Casperdroid5/ATTiny-Keychain-Handheld/Potential OLED drivers/ssd1306xled-master/ssd1306xled_imgs1/main.c

/**
 * SSD1306xLED - Testing scripts
 * @author Neven Boyanov
 * This is part of the Tinusaur/SSD1306xLED project.
 * ----------------------------------------------------------------------------
 *  Copyright (c) 2021 Tinusaur (https://tinusaur.com). All rights reserved.
 *  Distributed as open source under the MIT License (see the LICENSE.txt file)
 *  Please, retain in your work a link to the Tinusaur project website.
 * ----------------------------------------------------------------------------
 * Source code available at: https://gitlab.com/tinusaur/ssd1306xled
 */

// ============================================================================

// NOTE: About F_CPU - it should be set in either (1) Makefile; or (2) in the IDE.

#include <stdint.h>
#include <avr/io.h>
#include <util/delay.h>

#include "tinyavrlib/cpufreq.h"

#include "ssd1306xled/ssd1306xled.h"
#include "ssd1306xled/ssd1306xledfx.h"

#include "img0s128x64c1.h"
#include "img1s128x64c1.h"

// ~~~~~~~~~~~~~~~~~~~~~~~~~~~~~~~~~~~~~~~~~~~~~~~~~~~~~~~~~~~~~~~~~~~~~~~~~~~~
//                 ATtiny85
//               +----------+    (-)--GND--
//      (RST)--> + PB5  Vcc +----(+)--VCC--
// ---[OWOWOD]---+ PB3  PB2 +----[TWI/SCL]-
// --------------+ PB4  PB1 +--------------
// --------(-)---+ GND  PB0 +----[TWI/SDA]-
//               +----------+
//                 Tinusaur
// ~~~~~~~~~~~~~~~~~~~~~~~~~~~~~~~~~~~~~~~~~~~~~~~~~~~~~~~~~~~~~~~~~~~~~~~~~~~~
// NOTE: If you want to reassign the SCL and SDA pins and the I2C address
// do that in the library source code and recompile it so it will take affect.

// ----------------------------------------------------------------------------

#define TESTING_DELAY 500

int main(void) {

// ---- CPU Frequency Setup ----
#if F_CPU == 1000000UL
#pragma message "F_CPU=1MHZ"
	CLKPR_SET(CLKPR_1MHZ);
#elif F_CPU == 8000000UL
#pragma message "F_CPU=8MHZ"
	CLKPR_SET(CLKPR_8MHZ);
#else
#pragma message "F_CPU=????"
#error "CPU frequency should be either 1 MHz or 8 MHz"
#endif

	// ---- Initialization ----
	_delay_ms(40);	// Small delay might be necessary if ssd1306_init is the first operation in the application.
	ssd1306_init();

	// ---- Main Loop ----
	for (;;) {
		ssd1306_clear();	// Clear the screen.

		// ---- Draw bitmap on the screen ----
		ssd1306_draw_bmp(0, 0, 128, 8, img0s128x64c1);
		_delay_ms(TESTING_DELAY << 2);

		// ---- Draw bitmap on the screen ----
		ssd1306_draw_bmp(0, 0, 128, 8, img1s128x64c1);
		_delay_ms(TESTING_DELAY << 4);
	}

	return 0; // Return the mandatory for the "main" function int value - "0" for success.
}

// ============================================================================
